Herrera-Dev/PirCam_TelegramBot_ESPCAM/Proxy_Video_ESP32.py

import os, io, time, socket, subprocess, requests, imagehash
from flask import Flask, Response, stream_with_context, render_template
from datetime import datetime
from plyer import notification
from PIL import Image

status = True
MDNS = "espcam-bot"     # Nombre del host ESPmDNS de la esp32-cam, http://espcam-bot.local
SOLO_HOST = True        # True: solo desde localhost, False: acceso en toda la red local

duracion = 60  # Segundos de grabación del video.
velocidad = 7  # FPS para renderizar el video.
PauseMov = 15  # Pausar luego de detectar movimiento.
calMov = 2     # Sensibilidad de movimiento.

# -------------------------
app = Flask(__name__)

def resolve_mdns(hostname):
    try:
        return socket.gethostbyname(f"{hostname}.local")
    except socket.gaierror:
        return None

def buscar_ip(mdns):
    print(f"\n------------------------------")
    print(f"🔍 Buscando ESP32-CAM...")
    ip = resolve_mdns(mdns)
    while ip is None:
        ip = resolve_mdns(mdns)
        print(f"❌ No se encontró el dispositivo.")
        time.sleep(4)
    print(f"🌐 Abrir: http://localhost:5000")
    print(f"🏠 Solo localHost: {SOLO_HOST}")
    return ip

ESP32_IP = buscar_ip(MDNS)
@app.route("/stream")
def proxy_mjpeg():
    def generate(status):
        last_data_time = time.time()
        last_hash = None
        buffer = b""
        cooldown = 0

        while True:
            try:
                with requests.get(f"http://{ESP32_IP}/video", stream=True, timeout=5) as r:
                    r.raise_for_status()

                    if status:
                        print("* ✅ RUNNING: Streaming")
                        status = False

                    for chunk in r.iter_content(chunk_size=1024):
                        if not chunk:
                            if time.time() - last_data_time > 5:
                                raise RuntimeError("ESP32-CAM no está enviando datos")
                            continue

                        buffer += chunk
                        last_data_time = time.time()

                        # Buscar inicio y fin de un frame JPEG
                        start = buffer.find(b"\xff\xd8")
                        end = buffer.find(b"\xff\xd9")

                        if start != -1 and end != -1 and end > start:
                            frame_data = buffer[start:end + 2]
                            buffer = buffer[end + 2:]

                            try:
                                img = Image.open(io.BytesIO(frame_data)).convert("L")
                                current_hash = imagehash.phash(img)

                                if last_hash is not None:
                                    diff = abs(current_hash - last_hash)
                                    if diff > calMov and time.time() - cooldown > PauseMov:
                                        hora_actual = datetime.now().strftime("%H:%M:%S")
                                        print(f"[{hora_actual}] Movimiento detectado 📸")

                                        # Notificación de escritorio
                                        notification.notify(title="📸 Movimiento Detectado", message=f"Detectado a las {hora_actual}", timeout=5)

                                        # Sonido de alerta
                                        if os.name == "posix":  # Linux
                                            os.system('paplay /usr/share/sounds/freedesktop/stereo/complete.oga')
                                        elif os.name == "nt":   # Windows
                                            import winsound
                                            winsound.Beep(1000, 500)

                                        cooldown = time.time() 

                                last_hash = current_hash

                                # Enviar frame al cliente
                                yield (
                                    b"--123456789000000000000987654321\r\n"
                                    b"Content-Type: image/jpeg\r\n\r\n" +
                                    frame_data + b"\r\n"
                                )

                            except Exception as e:
                                print(f"Error procesando frame: {e}")
                                continue

            except Exception as e:
                print(f"* ❌ ERROR...")
                # print(f"* ❌ ERROR: {e}")
                # Mostrar frame vacío temporal mientras se reconecta
                yield (
                    b"--123456789000000000000987654321\r\n"
                    b"Content-Type: image/jpeg\r\n\r\n"
                    b"\xff\xd8\xff\xe0\x00\x10\x4a\x46\x49\x46\x00\x01\x01\x01\x00\x48\x00\x48\x00\x00\xff\xdb\x00\x43\x00\x03\x02\x02\x03\x02\x02\x03\x03\x03\x03\x04\x03\x03\x04\x05\x08\x05\x05\x04\x04\x05\x0a\x07\x07\x06\x08\x0c\x0a\x0c\x0c\x0b\x0a\x0b\x0b\x0d\x0e\x12\x10\x0d\x0e\x11\x0e\x0b\x0b\x10\x16\x10\x11\x13\x14\x15\x15\x15\x0c\x0f\x17\x18\x16\x14\x18\x12\x14\x15\x14\xff\xc0\x00\x0b\x08\x00\x01\x00\x01\x01\x01\x11\x00\xff\xc4\x00\x14\x00\x01\x00\x00\x00\x00\x00\x00\x00\x00\x00\x00\x00\x00\x00\x00\x00\x00\xff\xda\x00\x08\x01\x01\x00\x00\x3f\x00\xff\xd9"
                    b"\r\n"
                )
                # Notificación de escritorio
                notification.notify(title="❌ Error de video", message=f"Sin conexion {hora_actual}", timeout=5)
                status = True
                time.sleep(15)

    headers = {
        "Content-Type": "multipart/x-mixed-replace; boundary=123456789000000000000987654321",
        "Access-Control-Allow-Origin": "*",
    }
    return Response(stream_with_context(generate(status)), headers=headers)

@app.route("/")
def index():
    h = "localhost" if SOLO_HOST else "Red local"
    return render_template("index.html", esp32_ip=ESP32_IP, tipo_host=h)

@app.route("/grabar")
def grabar_fragmento():
    import os
    import re
    from datetime import datetime

    timestamp = datetime.now().strftime("%H%M%S_%Y")
    mjpg_file = f"recorded_videos/temp_{timestamp}.mjpg"
    mp4_file = f"recorded_videos/video_{timestamp}.mp4"
    url_stream = "http://localhost:5000/stream"

    try:
        inicio = time.time()
        with requests.get(url_stream, stream=True, timeout=5) as r:
            r.raise_for_status()
            with open(mjpg_file, "wb") as f:
                while time.time() - inicio < duracion:
                    chunk = r.raw.read(1024)
                    if not chunk:
                        break
                    f.write(chunk)

        tiempo_real = time.time() - inicio

        result = subprocess.run([
            "ffmpeg", "-y",
            "-r", str(velocidad),
            "-f", "mjpeg",
            "-i", mjpg_file,
            "-c:v", "libx264",
            "-pix_fmt", "yuv420p",
            "-r", str(velocidad),
            mp4_file
        ], capture_output=True, text=True)

        import re
        log_output = result.stderr
        matches = re.findall(r"frame=\s*(\d+)", log_output)
        frames = int(matches[-1]) if matches else 0

        os.remove(mjpg_file)
        fps_real = frames / tiempo_real if tiempo_real > 0 else 0

        return f"""
        ✅ Grabación finalizada<br>
        ⏱ Duración aprox.: {round(tiempo_real)} seg.<br>
        🎞️ Fotogramas: {frames}<br>
        📈 Esp32-Cam.: {round(fps_real)} FPS aprox.<br>
        📁 Archivo: <a href="/{mp4_file}" target="_blank">{mp4_file}</a>
        """

    except Exception as e:
        return f"❌ Error al grabar: {e}"

if __name__ == "__main__":
    host = "localhost" if SOLO_HOST else "0.0.0.0"
    app.run(host=host, port=5000)
